Gralerfics/ZeptoWatch/Documents/imgs/20221127045030.png

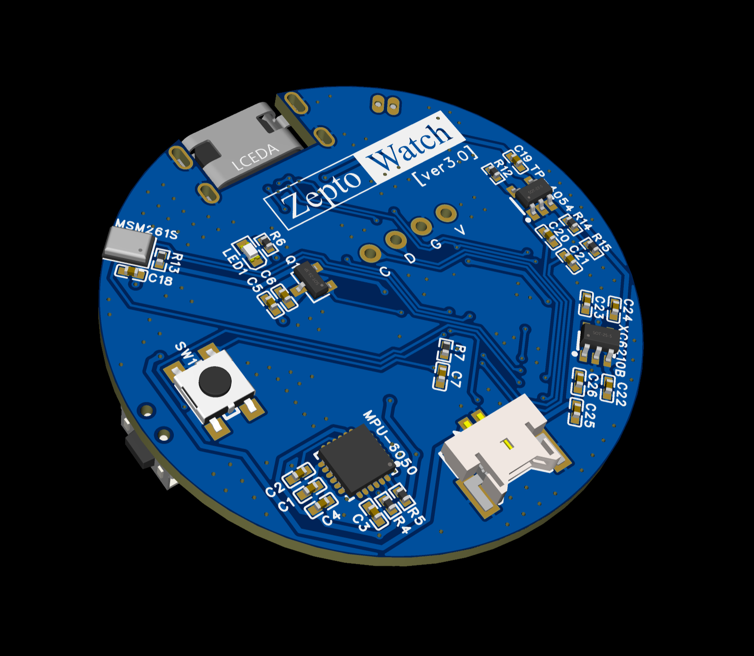
Documents/imgs/20221127045030.png
