Gralerfics/ZeptoWatch/Documents/imgs/20221127045100.png

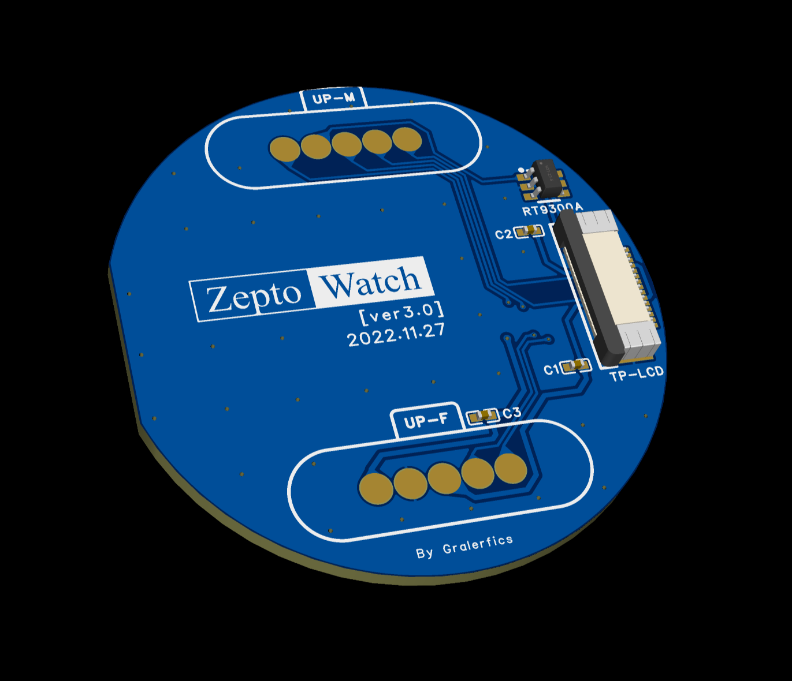
Documents/imgs/20221127045100.png
