Gralerfics/ZeptoWatch/Documents/imgs/20221127045136.png

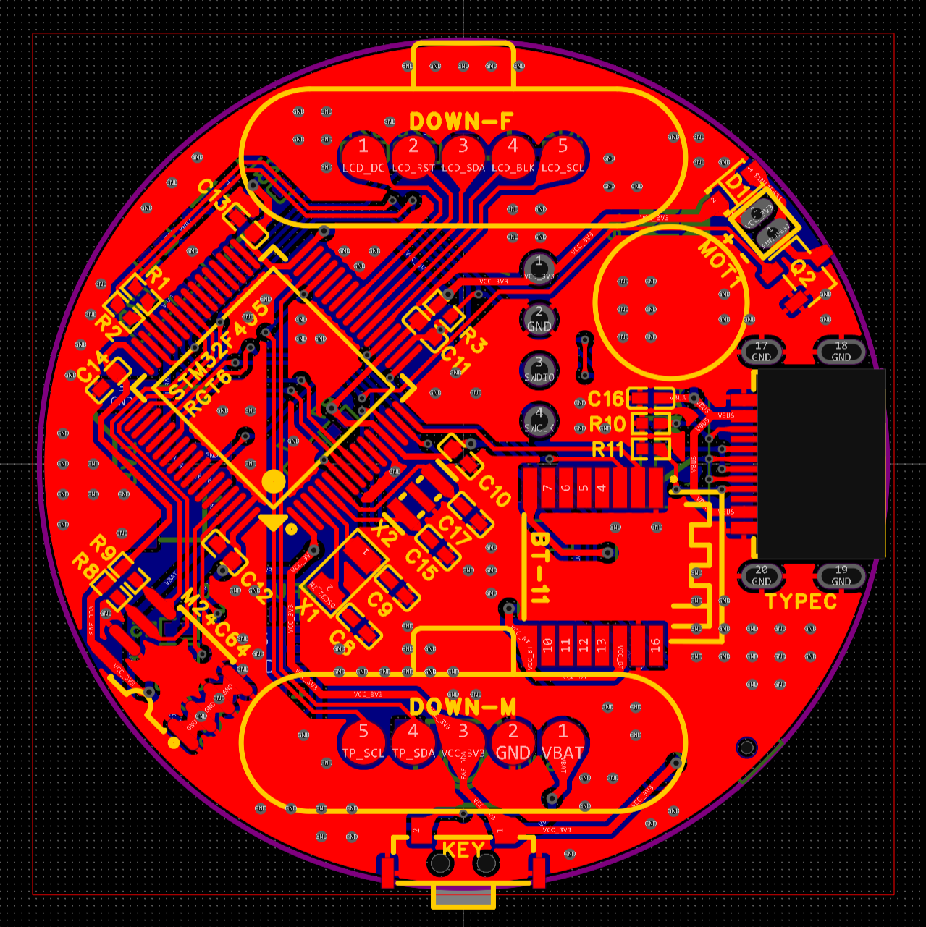
Documents/imgs/20221127045136.png
