Gralerfics/ZeptoWatch/Documents/imgs/IMG_20221120_230033.jpg

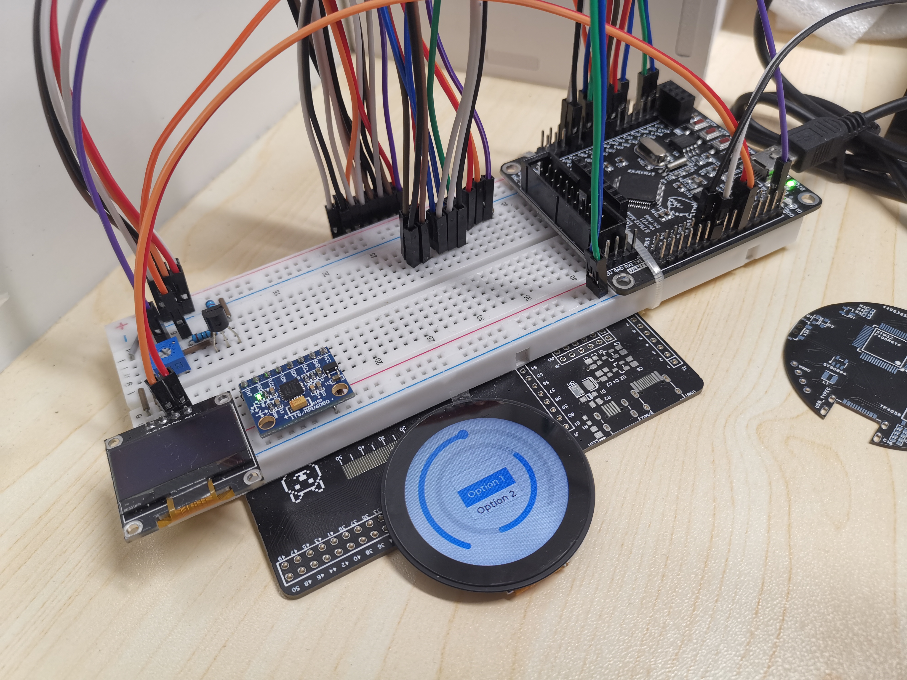
Documents/imgs/IMG_20221120_230033.jpg
