Gralerfics/ZeptoWatch/Documents/imgs/IMG_20221120_231222.png

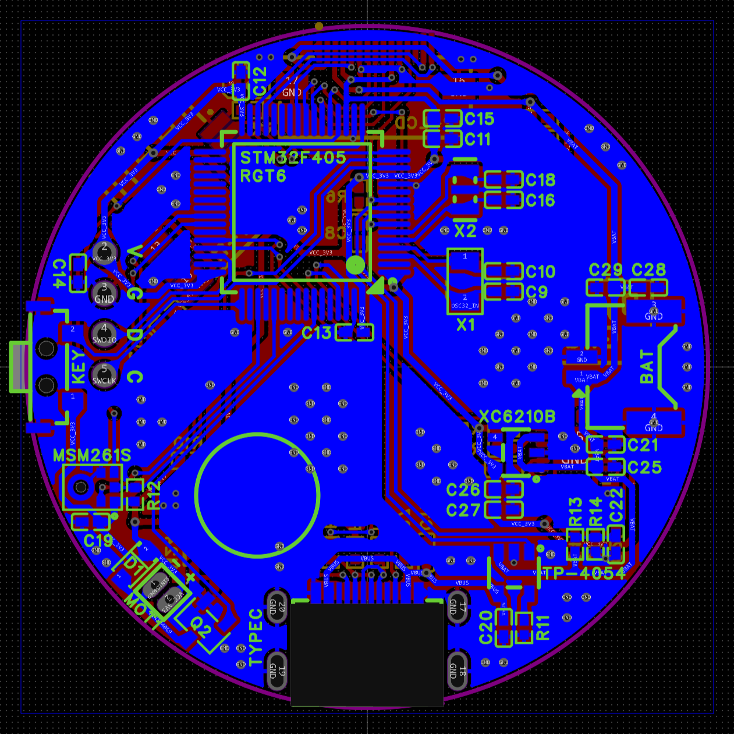
Documents/imgs/IMG_20221120_231222.png
