Gralerfics/ZeptoWatch/Documents/imgs/IMG_20221127_045317.jpg

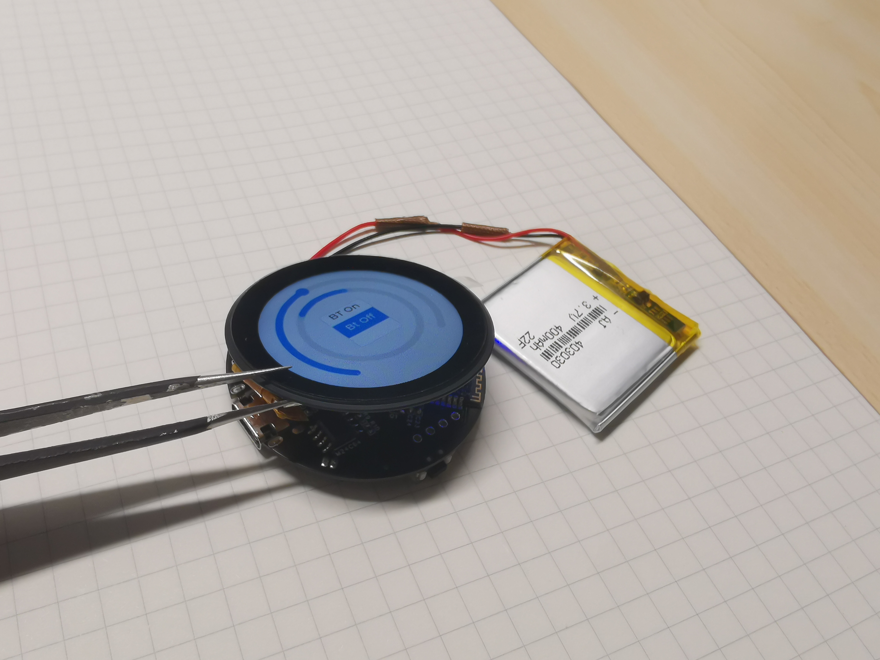
Documents/imgs/IMG_20221127_045317.jpg
