Gralerfics/ZeptoWatch/Documents/imgs/IMG_20221211_184247.jpg

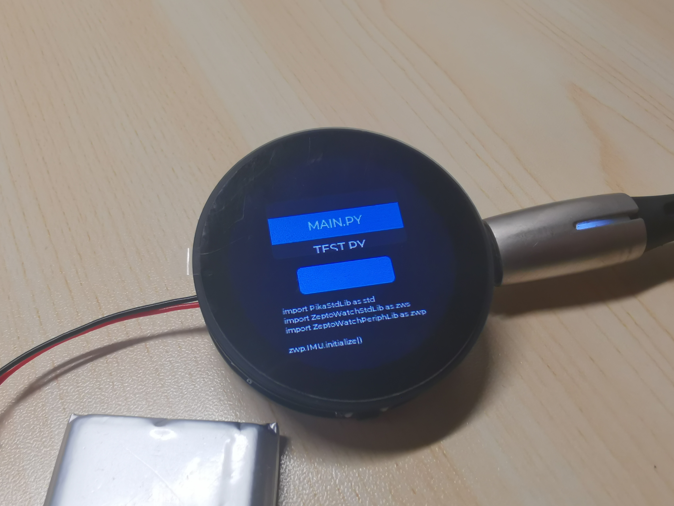
Documents/imgs/IMG_20221211_184247.jpg
