Gralerfics/ZeptoWatch/Structure/img/home.png

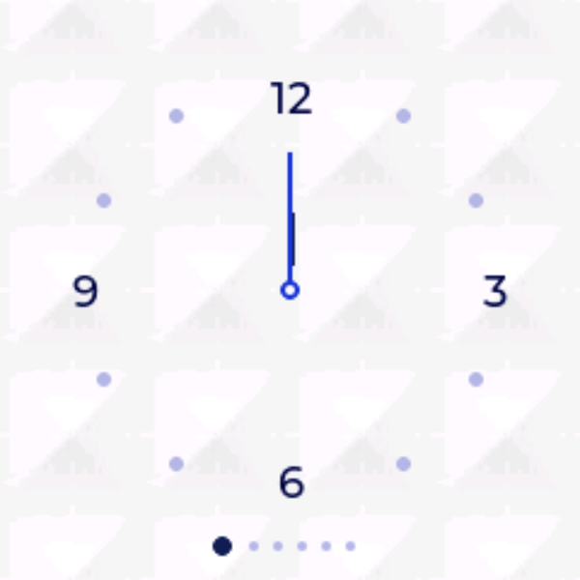
Structure/img/home.png
