Gralerfics/ZeptoWatch/Structure/img/lcd_1.png

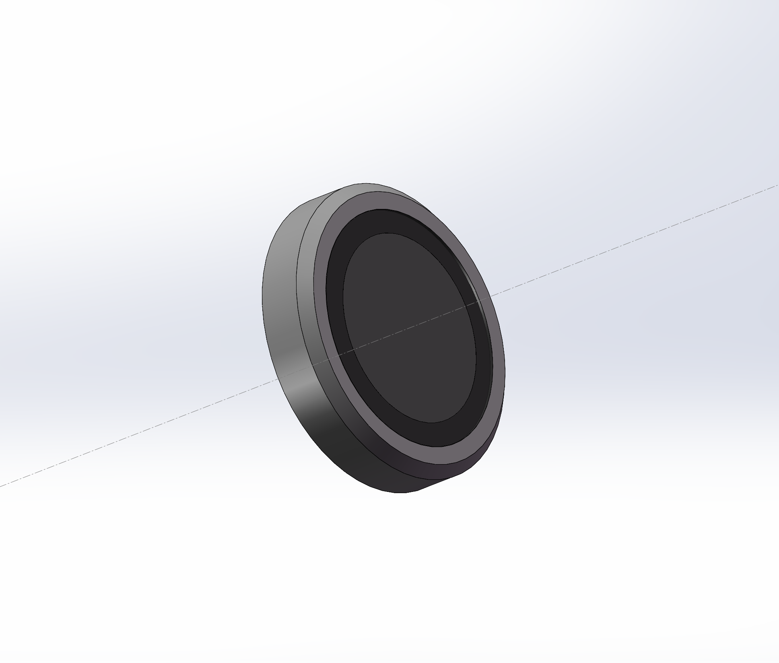
Structure/img/lcd_1.png
