Gralerfics/ZeptoWatch/Structure/img/lcd_boom_1.png

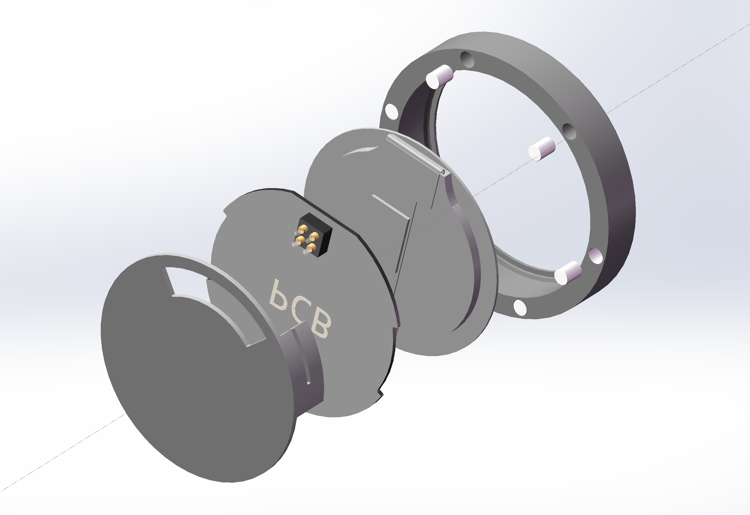
Structure/img/lcd_boom_1.png
