Gralerfics/ZeptoWatch/Structure/img/lcd_boom_3.png

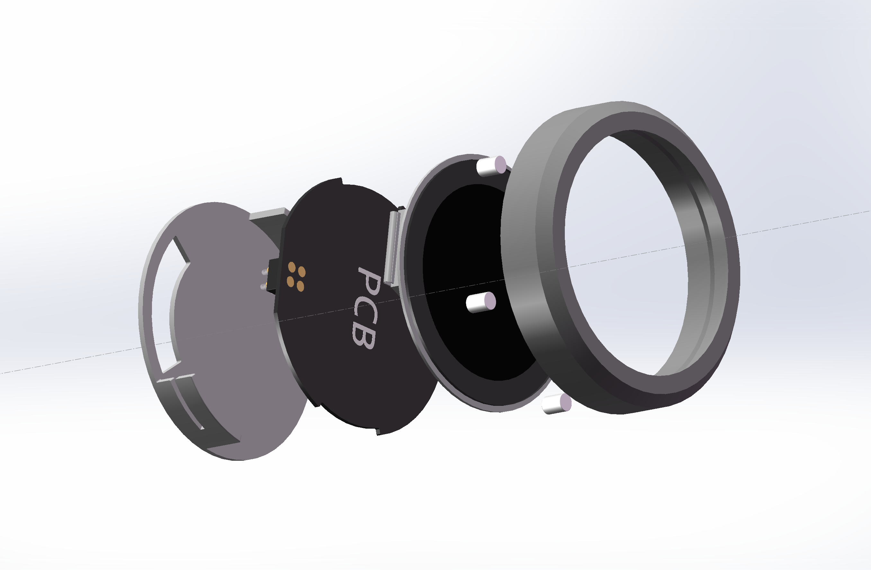
Structure/img/lcd_boom_3.png
