Gralerfics/ZeptoWatch/Structure/img/test_1.png

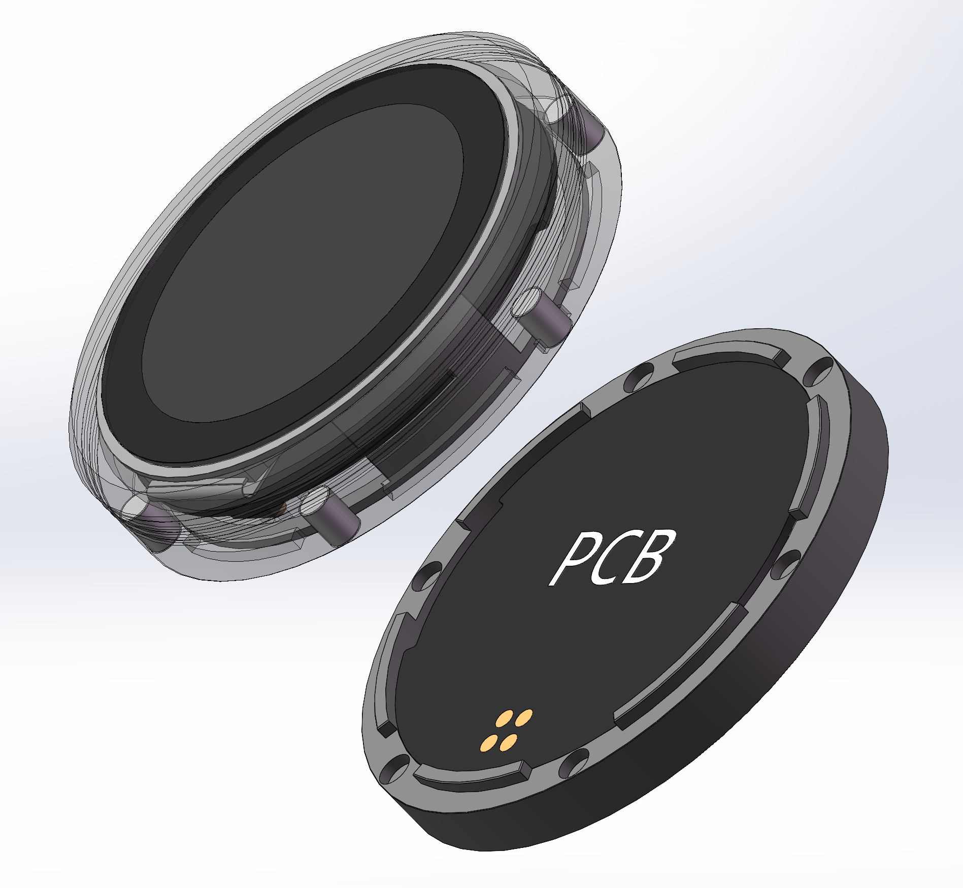
Structure/img/test_1.png
