Gralerfics/ZeptoWatch/Firmware/ZeptoWatch/ZeptoWatch/Drivers/battery/battery.h

#ifndef __BATTERY_H
#define __BATTERY_H

#ifdef __cplusplus
extern "C" {
#endif

#include "common.h"

/*
 * BAT_CHRG_R -> PC1
 */

#define __HAL_RCC_BAT_CHRG_R_CLK_ENABLE() __HAL_RCC_GPIOC_CLK_ENABLE()
#define BAT_CHRG_R_GPIO_Port GPIOC
#define BAT_CHRG_R_Pin GPIO_PIN_1
#define BAT_FILTERING_PARAM 10

void Battery_Init();
void Battery_StartSampling();
void Battery_StopSampling();

int Battery_IsCharging();
uint16_t Battery_GetADCData();
int Battery_GetPowerPercentage();

#ifdef __cplusplus
}
#endif

#endif
