Gralerfics/ZeptoWatch/Firmware/ZeptoWatch/Core/Src/rtc.c

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
/* Includes ------------------------------------------------------------------*/
#include "rtc.h"

/* USER CODE BEGIN 0 */
#include "clock.h"
/* USER CODE END 0 */

RTC_HandleTypeDef hrtc;

/* RTC init function */
void MX_RTC_Init(void)
{

	RTC_TimeTypeDef sTime = {0};
	RTC_DateTypeDef sDate = {0};
	RTC_AlarmTypeDef sAlarm = {0};

	/** Initialize RTC Only
	*/
	hrtc.Instance = RTC;
	hrtc.Init.HourFormat = RTC_HOURFORMAT_24;
	hrtc.Init.AsynchPrediv = 127;
	hrtc.Init.SynchPrediv = 255;
	hrtc.Init.OutPut = RTC_OUTPUT_DISABLE;
	hrtc.Init.OutPutPolarity = RTC_OUTPUT_POLARITY_HIGH;
	hrtc.Init.OutPutType = RTC_OUTPUT_TYPE_OPENDRAIN;
	if (HAL_RTC_Init(&hrtc) != HAL_OK)
	{
		Error_Handler();
	}

	/* USER CODE BEGIN Check_RTC_BKUP */
	HAL_RTC_GetTime(&hrtc, &RTC_Time, RTC_FORMAT_BIN);
	HAL_RTC_GetDate(&hrtc, &RTC_Date, RTC_FORMAT_BIN);
	goto SkipTimeInitialization;
	// TODO: 更新 CubeMX 记得优先级提高
	/* USER CODE END Check_RTC_BKUP */

	/** Initialize RTC and set the Time and Date
	*/
	sTime.Hours = 0;
	sTime.Minutes = 0;
	sTime.Seconds = 0;
	sTime.DayLightSaving = RTC_DAYLIGHTSAVING_NONE;
	sTime.StoreOperation = RTC_STOREOPERATION_RESET;
	if (HAL_RTC_SetTime(&hrtc, &sTime, RTC_FORMAT_BIN) != HAL_OK)
	{
		Error_Handler();
	}
	sDate.WeekDay = RTC_WEEKDAY_MONDAY;
	sDate.Month = RTC_MONTH_JANUARY;
	sDate.Date = 1;
	sDate.Year = 0;

	if (HAL_RTC_SetDate(&hrtc, &sDate, RTC_FORMAT_BIN) != HAL_OK)
	{
		Error_Handler();
	}

	/** Enable the Alarm A
	*/
	sAlarm.AlarmTime.Hours = 0;
	sAlarm.AlarmTime.Minutes = 0;
	sAlarm.AlarmTime.Seconds = 1;
	sAlarm.AlarmTime.SubSeconds = 0;
	sAlarm.AlarmTime.DayLightSaving = RTC_DAYLIGHTSAVING_NONE;
	sAlarm.AlarmTime.StoreOperation = RTC_STOREOPERATION_RESET;
	sAlarm.AlarmMask = RTC_ALARMMASK_DATEWEEKDAY|RTC_ALARMMASK_HOURS
					   |RTC_ALARMMASK_MINUTES;
	sAlarm.AlarmSubSecondMask = RTC_ALARMSUBSECONDMASK_ALL;
	sAlarm.AlarmDateWeekDaySel = RTC_ALARMDATEWEEKDAYSEL_DATE;
	sAlarm.AlarmDateWeekDay = 1;
	sAlarm.Alarm = RTC_ALARM_A;
	if (HAL_RTC_SetAlarm_IT(&hrtc, &sAlarm, RTC_FORMAT_BIN) != HAL_OK)
	{
		Error_Handler();
	}
	/* USER CODE BEGIN RTC_Init 2 */
	SkipTimeInitialization:
	sAlarm.AlarmTime.Hours = 0;
	sAlarm.AlarmTime.Minutes = 0;
	sAlarm.AlarmTime.Seconds = RTC_Time.Seconds + 1;
	sAlarm.AlarmTime.SubSeconds = 0;
	sAlarm.AlarmTime.DayLightSaving = RTC_DAYLIGHTSAVING_NONE;
	sAlarm.AlarmTime.StoreOperation = RTC_STOREOPERATION_RESET;
	sAlarm.AlarmMask = RTC_ALARMMASK_DATEWEEKDAY|RTC_ALARMMASK_HOURS
					   |RTC_ALARMMASK_MINUTES;
	sAlarm.AlarmSubSecondMask = RTC_ALARMSUBSECONDMASK_ALL;
	sAlarm.AlarmDateWeekDaySel = RTC_ALARMDATEWEEKDAYSEL_DATE;
	sAlarm.AlarmDateWeekDay = 1;
	sAlarm.Alarm = RTC_ALARM_A;
	if (HAL_RTC_SetAlarm_IT(&hrtc, &sAlarm, RTC_FORMAT_BIN) != HAL_OK)
	{
		Error_Handler();
	}
	/* USER CODE END RTC_Init 2 */

}

void HAL_RTC_MspInit(RTC_HandleTypeDef* rtcHandle)
{

	RCC_PeriphCLKInitTypeDef PeriphClkInitStruct = {0};
	if(rtcHandle->Instance==RTC)
	{
		/** Initializes the peripherals clock
		*/
		PeriphClkInitStruct.PeriphClockSelection = RCC_PERIPHCLK_RTC;
		PeriphClkInitStruct.RTCClockSelection = RCC_RTCCLKSOURCE_LSE;
		if (HAL_RCCEx_PeriphCLKConfig(&PeriphClkInitStruct) != HAL_OK)
		{
			Error_Handler();
		}

		/* RTC clock enable */
		__HAL_RCC_RTC_ENABLE();

		/* RTC interrupt Init */
		HAL_NVIC_SetPriority(RTC_Alarm_IRQn, 6, 0);
		HAL_NVIC_EnableIRQ(RTC_Alarm_IRQn);
	}
}

void HAL_RTC_MspDeInit(RTC_HandleTypeDef* rtcHandle)
{

	if(rtcHandle->Instance==RTC)
	{
		/* Peripheral clock disable */
		__HAL_RCC_RTC_DISABLE();

		/* RTC interrupt Deinit */
		HAL_NVIC_DisableIRQ(RTC_Alarm_IRQn);
	}
}
